RobotCasserole1736/RoboSim/docs/Robot15/resources/viair90C_flow_rate.png

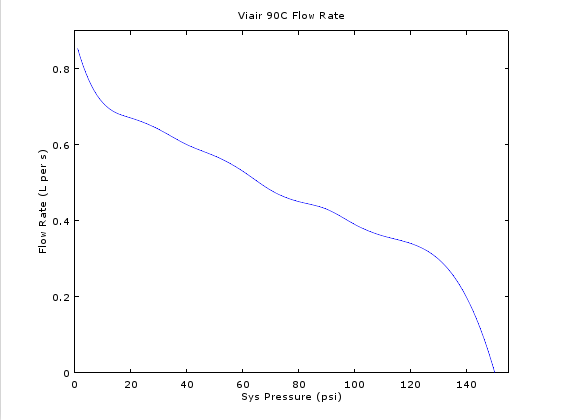
docs/Robot15/resources/viair90C_flow_rate.png
