RobotCasserole1736/RoboSim/Eagle/RoboSim/hat.bmp

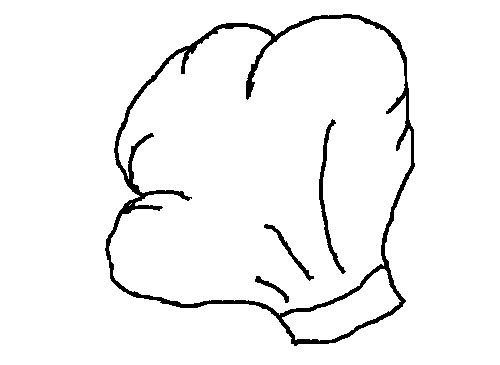
Eagle/RoboSim/hat.bmp
