RobotCasserole1736/RoboSim/PSPICE/Results/SlewTest.jpg

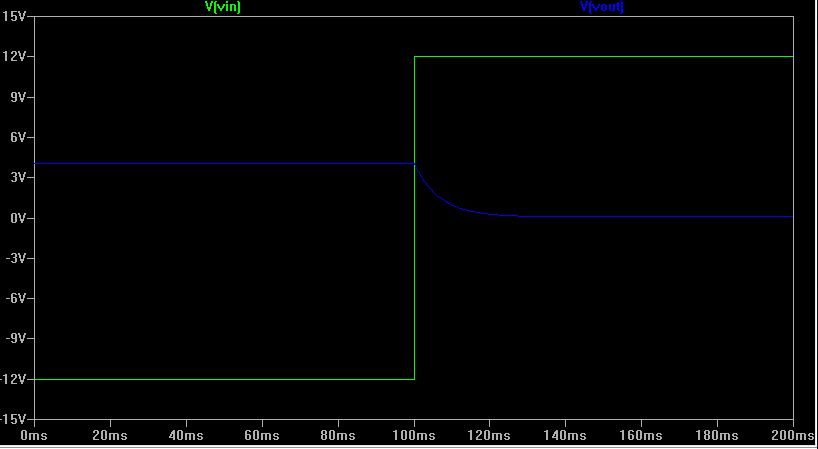
PSPICE/Results/SlewTest.jpg
