RobotCasserole1736/RoboSim/PSPICE/Results/Test1+12V50Pct.jpg

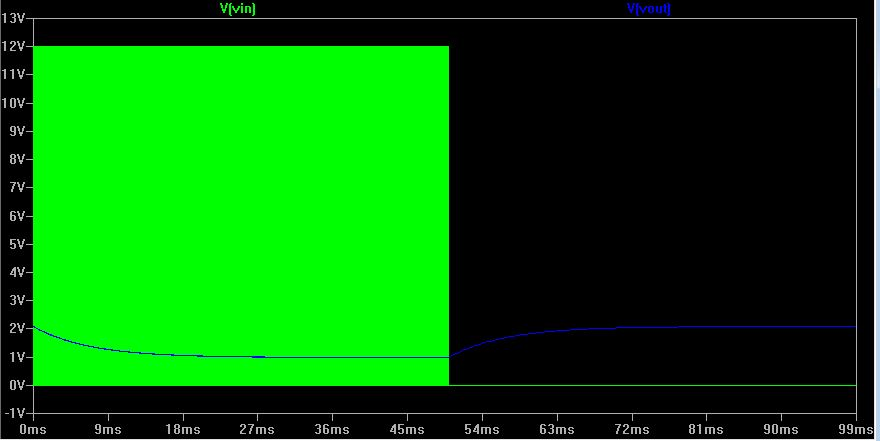
PSPICE/Results/Test1+12V50Pct.jpg
