RobotCasserole1736/RoboSim/PSPICE/RoboSim PWM Input Filter V2.asc

C2: cap; 0.5µF
MainSupply1: voltage; -30
MainSupply: voltage; 30
OffsetSupply: voltage; 2.5
PWMin: voltage; PULSE(0 12 0 0 0 0.00005555555 0.0000666666 1500)
Rfb: res; 9.4K
Rgnd: res; 9.4K
Rin1: res; 10K
Rin2: res; 10K
Rin+: res; 10K
Rin-: res; 10K
U1: LT1006
Named nets: Vcc, 0, Voff, Vdd
.tran 0.5
