RobotCasserole1736/RoboSim/ArduinoSrc_RTOS_Mega/RoboSim_rtos/os/heap_3.cpp

/*
    FreeRTOS V8.0.1 - Copyright (C) 2014 Real Time Engineers Ltd.
    All rights reserved

    VISIT http://www.FreeRTOS.org TO ENSURE YOU ARE USING THE LATEST VERSION.

    ***************************************************************************
     *                                                                       *
     *    FreeRTOS provides completely free yet professionally developed,    *
     *    robust, strictly quality controlled, supported, and cross          *
     *    platform software that has become a de facto standard.             *
     *                                                                       *
     *    Help yourself get started quickly and support the FreeRTOS         *
     *    project by purchasing a FreeRTOS tutorial book, reference          *
     *    manual, or both from: http://www.FreeRTOS.org/Documentation        *
     *                                                                       *
     *    Thank you!                                                         *
     *                                                                       *
    ***************************************************************************

    This file is part of the FreeRTOS distribution.

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
    >>!   NOTE: The modification to the GPL is included to allow you to     !<<
    >>!   distribute a combined work that includes FreeRTOS without being   !<<
    >>!   obliged to provide the source code for proprietary components     !<<
    >>!   outside of the FreeRTOS kernel.                                   !<<

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
    1 tab == 4 spaces!

    ***************************************************************************
     *                                                                       *
     *    Having a problem?  Start by reading the FAQ "My application does   *
     *    not run, what could be wrong?"                                     *
     *                                                                       *
     *    http://www.FreeRTOS.org/FAQHelp.html                               *
     *                                                                       *
    ***************************************************************************

    http://www.FreeRTOS.org - Documentation, books, training, latest versions,
    license and Real Time Engineers Ltd. contact details.

    http://www.FreeRTOS.org/plus - A selection of FreeRTOS ecosystem products,
    including FreeRTOS+Trace - an indispensable productivity tool, a DOS
    compatible FAT file system, and our tiny thread aware UDP/IP stack.

    http://www.OpenRTOS.com - Real Time Engineers ltd license FreeRTOS to High
    Integrity Systems to sell under the OpenRTOS brand.  Low cost OpenRTOS
    licenses offer ticketed support, indemnification and middleware.

    http://www.SafeRTOS.com - High Integrity Systems also provide a safety
    engineered and independently SIL3 certified version for use in safety and
    mission critical applications that require provable dependability.

    1 tab == 4 spaces!
*/


/*
 * Implementation of pvPortMalloc() and vPortFree() that relies on the
 * compilers own malloc() and free() implementations.
 *
 * This file can only be used if the linker is configured to to generate
 * a heap memory area.
 *
 * See heap_1.c, heap_2.c and heap_4.c for alternative implementations, and the
 * memory management pages of http://www.FreeRTOS.org for more information.
 */

#include "Arduino.h"
#include <stdlib.h>


/* Defining MPU_WRAPPERS_INCLUDED_FROM_API_FILE prevents task.h from redefining
all the API functions to use the MPU wrappers.  That should only be done when
task.h is included from an application file. */
#define MPU_WRAPPERS_INCLUDED_FROM_API_FILE

#include "FreeRTOS.h"
#include "task.h"

#undef MPU_WRAPPERS_INCLUDED_FROM_API_FILE

/*-----------------------------------------------------------*/
extern "C"{
void *pvPortMalloc( size_t xWantedSize )
{
	void *pvReturn;

	vTaskSuspendAll();
	{
		pvReturn = malloc( xWantedSize );
		traceMALLOC( pvReturn, xWantedSize );
		#ifdef PVPORTMALLOC_DEBUG_PRINT
		Serial.print("Malloc Called! - ");
		Serial.println(xWantedSize);
		#endif
	}
	( void ) xTaskResumeAll();

	#if( configUSE_MALLOC_FAILED_HOOK == 1 )
	{
		if( pvReturn == NULL )
		{
			extern void vApplicationMallocFailedHook( void );
			vApplicationMallocFailedHook();
		}
	}
	#endif

	return pvReturn;
}
/*-----------------------------------------------------------*/

void vPortFree( void *pv )
{
	if( pv )
	{
		vTaskSuspendAll();
		{
			free( pv );
			traceFREE( pv, 0 );
		}
		( void ) xTaskResumeAll();
	}
}
}
