RobotCasserole1736/RoboSim/ArduinoSrc_RTOS_Mega/RoboSim_rtos/main/memory_monitor.ino

/******************************************************************************/
/******************************************************************************/
/**   COPYRIGHT (C) FRC TEAM 1736 ROBOT CASSEROLE 2015 ALL RIGHTS RESERVED   **/
/******************************************************************************/
/******************************************************************************/
// RoboSim - an Arduino-based, Hardware-in-the-loop Robot simulation platform
//
// File: memory_monitor.ino
// Description:  - functions to calculate arduino runtime memory usage
//
//  Change History:
//      Chris Gerth - 04Oct2015 - Created
//
/******************************************************************************/


/******************************************************************************/
/** HEADER INCLUDES                                                          **/
/******************************************************************************/

#include "memory_monitor.h"

/******************************************************************************/
/** DATA DEFINITIONS                                                         **/
/******************************************************************************/
extern unsigned int __bss_end;
extern unsigned int __heap_start;
extern void *__brkval;

/******************************************************************************/
/** FUNCTIONS                                                                **/
/******************************************************************************/
int freeMemory() {
  int free_memory;

  if((int)__brkval == 0)
     free_memory = ((int)&free_memory) - ((int)&__bss_end);
  else
    free_memory = ((int)&free_memory) - ((int)__brkval);

  return free_memory;
}

double calc_memory_usage_pct()
{
    return ((double)(TOTAL_RAM-freeMemory()))/((double)TOTAL_RAM) * 100.0; //TBD - why the heck doesn't this work???
}
