RobotCasserole1736/RoboSim/ArduinoSrc_RTOS_Mega/RoboSim_rtos/main/plant.h

/******************************************************************************/
/******************************************************************************/
/**   COPYRIGHT (C) FRC TEAM 1736 ROBOT CASSEROLE 2015 ALL RIGHTS RESERVED   **/
/******************************************************************************/
/******************************************************************************/
// RoboSim - an Arduino-based, Hardware-in-the-loop Robot simulation platform
//
// File: plant.h
// Description:  - Main plant function for emulating robot functionality
//
//  Change History:
//      Chris Gerth - 20Mar2015 - Created
//
/******************************************************************************/
#ifndef PLANT_h
#define PLANT_h

/******************************************************************************/
/** HEADER INCLUDES                                                          **/
/******************************************************************************/
#include "plantConfig.h"

/******************************************************************************/
/** DATA DEFINITIONS                                                         **/
/******************************************************************************/

/******************************************************************************/
/** FUNCTION HEADERS                                                         **/
/******************************************************************************/
void plant_periodic_loop();

#endif /*PLANT_h */
