RobotCasserole1736/RoboSim/ArduinoSrc_RTOS_Mega/RoboSim_rtos/main/plantConfig.h

/******************************************************************************/
/******************************************************************************/
/**   COPYRIGHT (C) FRC TEAM 1736 ROBOT CASSEROLE 2015 ALL RIGHTS RESERVED   **/
/******************************************************************************/
/******************************************************************************/
// RoboSim - an Arduino-based, Hardware-in-the-loop Robot simulation platform
//
// File: pllantConfig.h
// Description:  - Configuration paramaters relevant to the behavior of the
//                 robot's plant model
//
//  Change History:
//      Chris Gerth - 20Mar2015 - Created
//
/******************************************************************************/
/******************************************************************************/
#ifndef PLANTCONFIG_h
#define PLANTCONFIG_h

/******************************************************************************/
/** HEADER INCLUDES                                                          **/
/******************************************************************************/

/******************************************************************************/
/** DATA DEFINITIONS                                                         **/
/******************************************************************************/

/******************************************************************************/
/** FUNCTION PROTOTYPES                                                      **/
/******************************************************************************/


#endif /*PLANTCONFIG_h*/
